vllogic/vllink_lite/doc/usb_interface.png

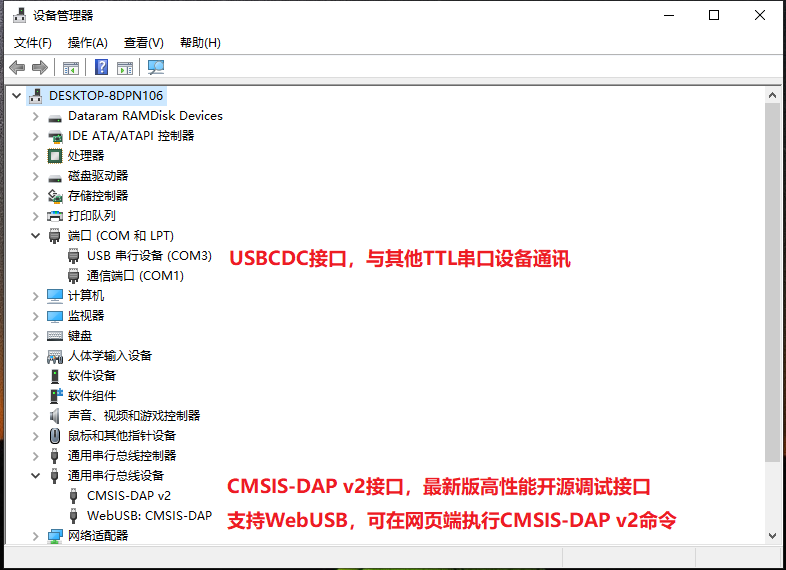
doc/usb_interface.png
