vllogic/vllink_lite/hardware/vllink_lite.r3/vllink_lite.r3.bottom.png

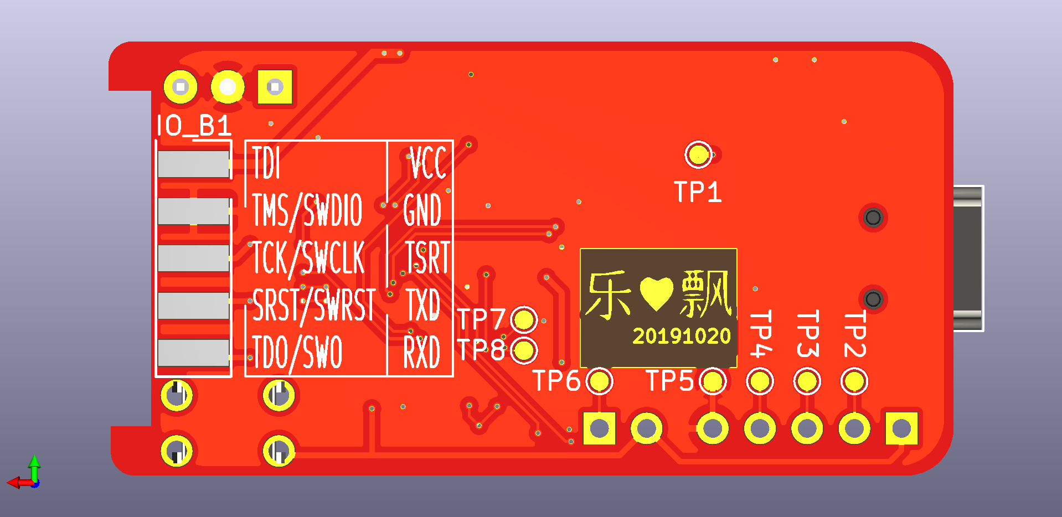
hardware/vllink_lite.r3/vllink_lite.r3.bottom.png
