vllogic/vllink_lite/vsf/vsf_private/hal/driver/GigaDevice/GD32E10X/driver.h

#if defined(__VSF_HEADER_ONLY_SHOW_ARCH_INFO__)

#   include "__device.h"

#else

#   ifndef __HAL_DRIVER_GIGADEVICE_GD32E10X_H__
#       define __HAL_DRIVER_GIGADEVICE_GD32E10X_H__

/*============================ INCLUDES ======================================*/

#       include "hal/vsf_hal_cfg.h"
#       include "./device.h"
#       include "./common/usb/usb.h"
#       include "./common/dma.h"
#       include "./common/flash.h"
#       include "./common/io.h"
#       include "./common/spi.h"
#       include "./common/usart.h"
#       include "./jtag.h"
#       include "./swd.h"
#       include "./timestamp.h"

/*============================ MACROS ========================================*/
/*============================ MACROFIED FUNCTIONS ===========================*/
/*============================ TYPES =========================================*/
/*============================ GLOBAL VARIABLES ==============================*/
/*============================ LOCAL VARIABLES ===============================*/
/*============================ PROTOTYPES ====================================*/

#   endif   // __HAL_DRIVER_GIGADEVICE_GD32E10X_H__
#endif      // __VSF_HEADER_ONLY_SHOW_ARCH_INFO__
/* EOF */
